mrbeam/Mr-Beam-Shield/MrBeamShield/MrBeamShield4.png

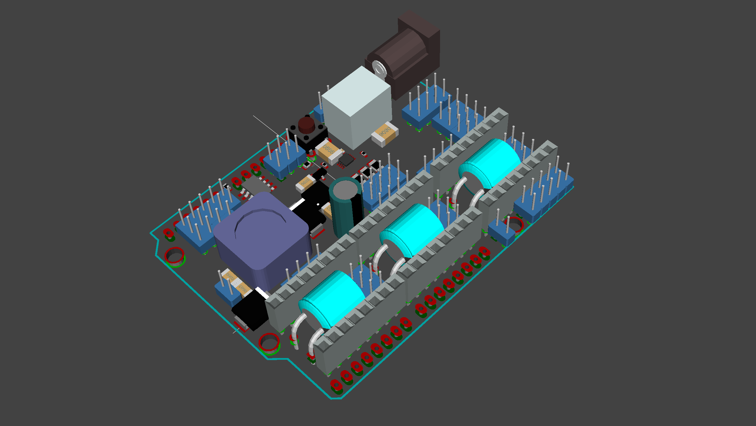
MrBeamShield/MrBeamShield4.png
