mrbeam/Mr-Beam-Shield/MrBeamShield/MrBeamShield5.png

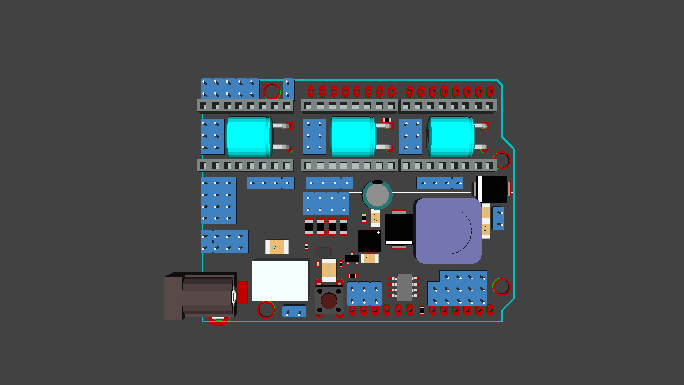
MrBeamShield/MrBeamShield5.png
