mrbeam/Mr-Beam-Shield/MrBeamShield/MrBeamShield_pwr.png

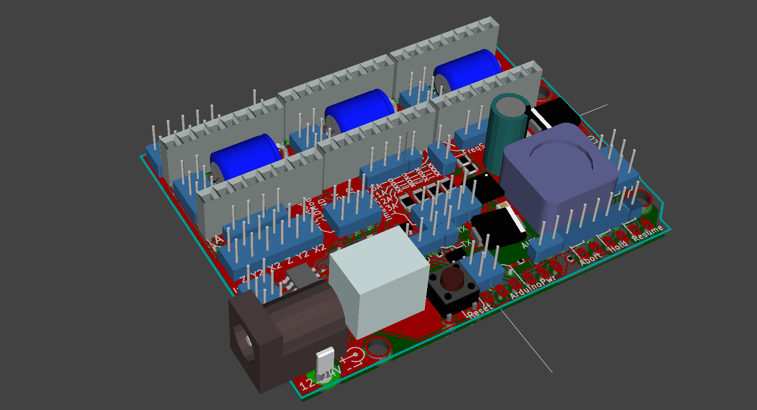
MrBeamShield/MrBeamShield_pwr.png
