mrbeam/Mr-Beam-Shield/MrBeamShield/MrBeamShield_xpololu.png

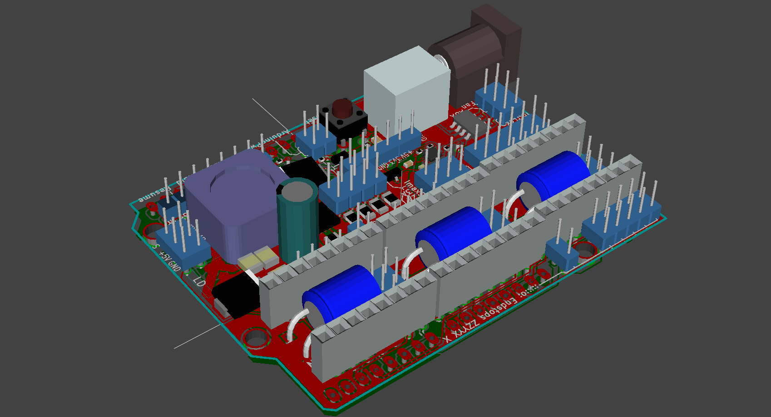
MrBeamShield/MrBeamShield_xpololu.png
